boert/KC85__M037_segmented_ROM/EPROM-Generator/romstart.h

/*
 * (c) 2020, 2024 Bert Lange
 *
 * EPROM-Generator für M037-Module (M045/M046/M047)
 * und M062 (32k/64k)
 *
 * Klasse für das eigentliche Hauptfenster
 */
#ifndef ROMSTART_H
#define ROMSTART_H

#include "ui_qtprogramm.h"
#include "modul.h"
#include "kcc.h"
#include "datamodel.h"
#include "delegate.h"
#include "previewselect.h"

#include <QItemSelectionModel>

class Romstart : public QMainWindow, public Ui::MainWindow
{
    Q_OBJECT

    public:
        Romstart( QMainWindow *parent = 0);
        ~Romstart();
        void add_files( QStringList);
        void update_modul_labels();

    private slots:
        void select_modul( int);

        void add_files();
        void remove_file( int);
        void recalcBlocks();
        void generate_EPROM();
        void exchange_preview();
        void update_preview( QItemSelection, QItemSelection);

    private:
        Delegate        m_delegate;
        Datamodel       m_model;
        Modul           m_modul;
        QPalette        m_palette_normal;
        QPalette        m_palette_full;
        QStatusBar      m_status;
        QLabel          m_copy_message;
        QStringList     m_modul_list = { "M045", "M046", "M047", "M062 (32k)", "M062 (64k)"};
};

#endif // ROMSTART_H
